Gravityy999/Proiect_InkTime/Hardware/Schematic_final.sch

## EAGLE design Hardware/Schematic_final.sch (2026-04-21)

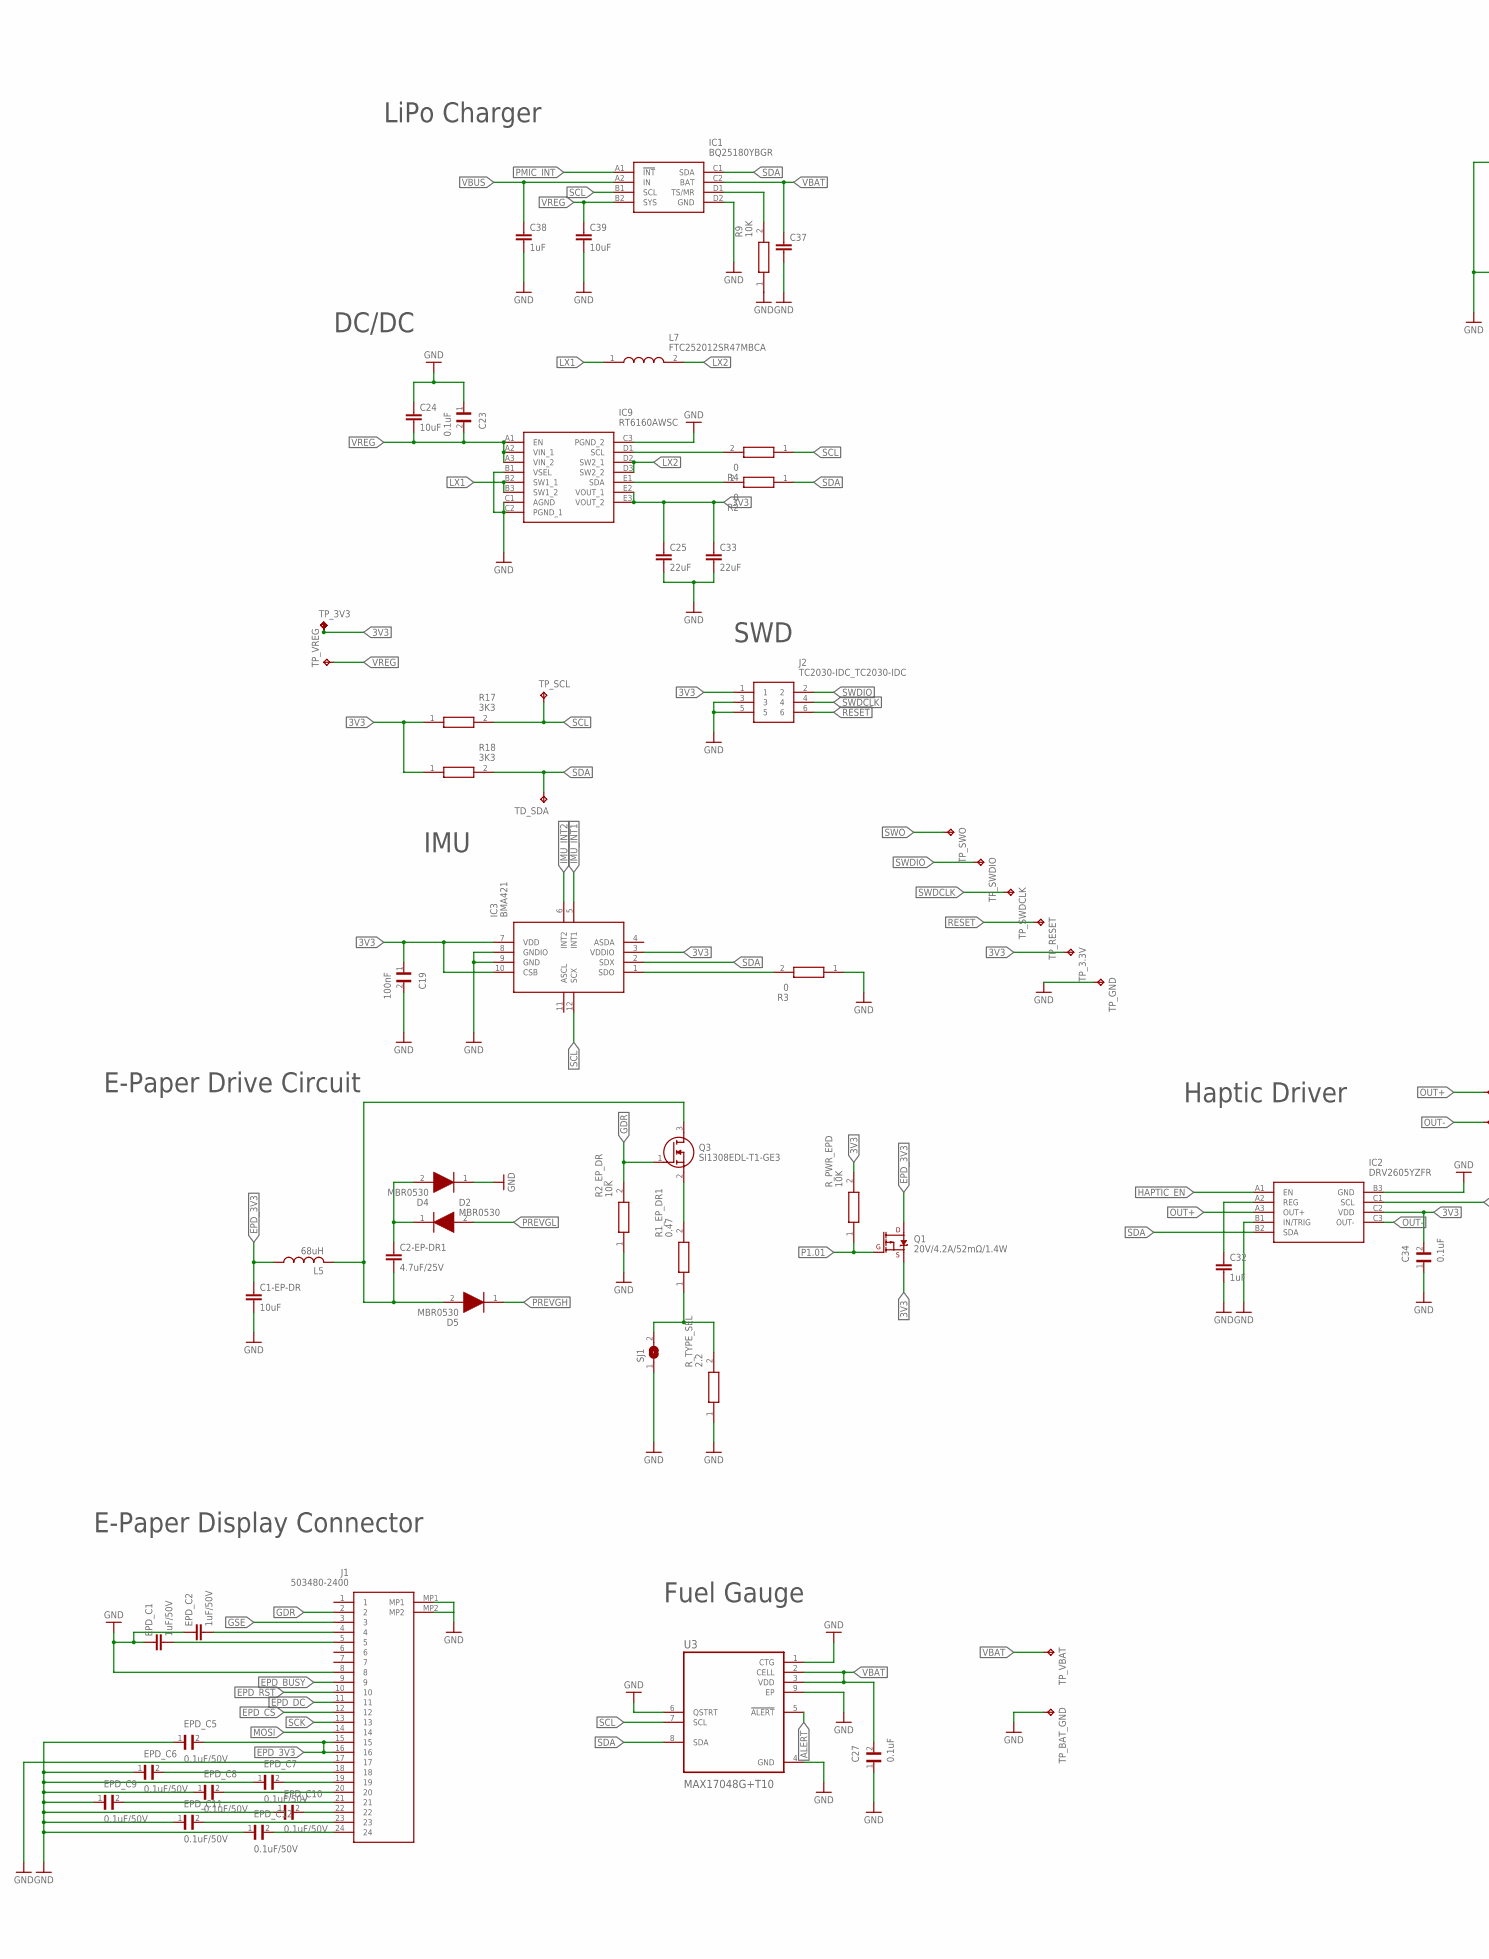
[picture p7: schematic Schematic_final.sch, part in row 1, column 1]

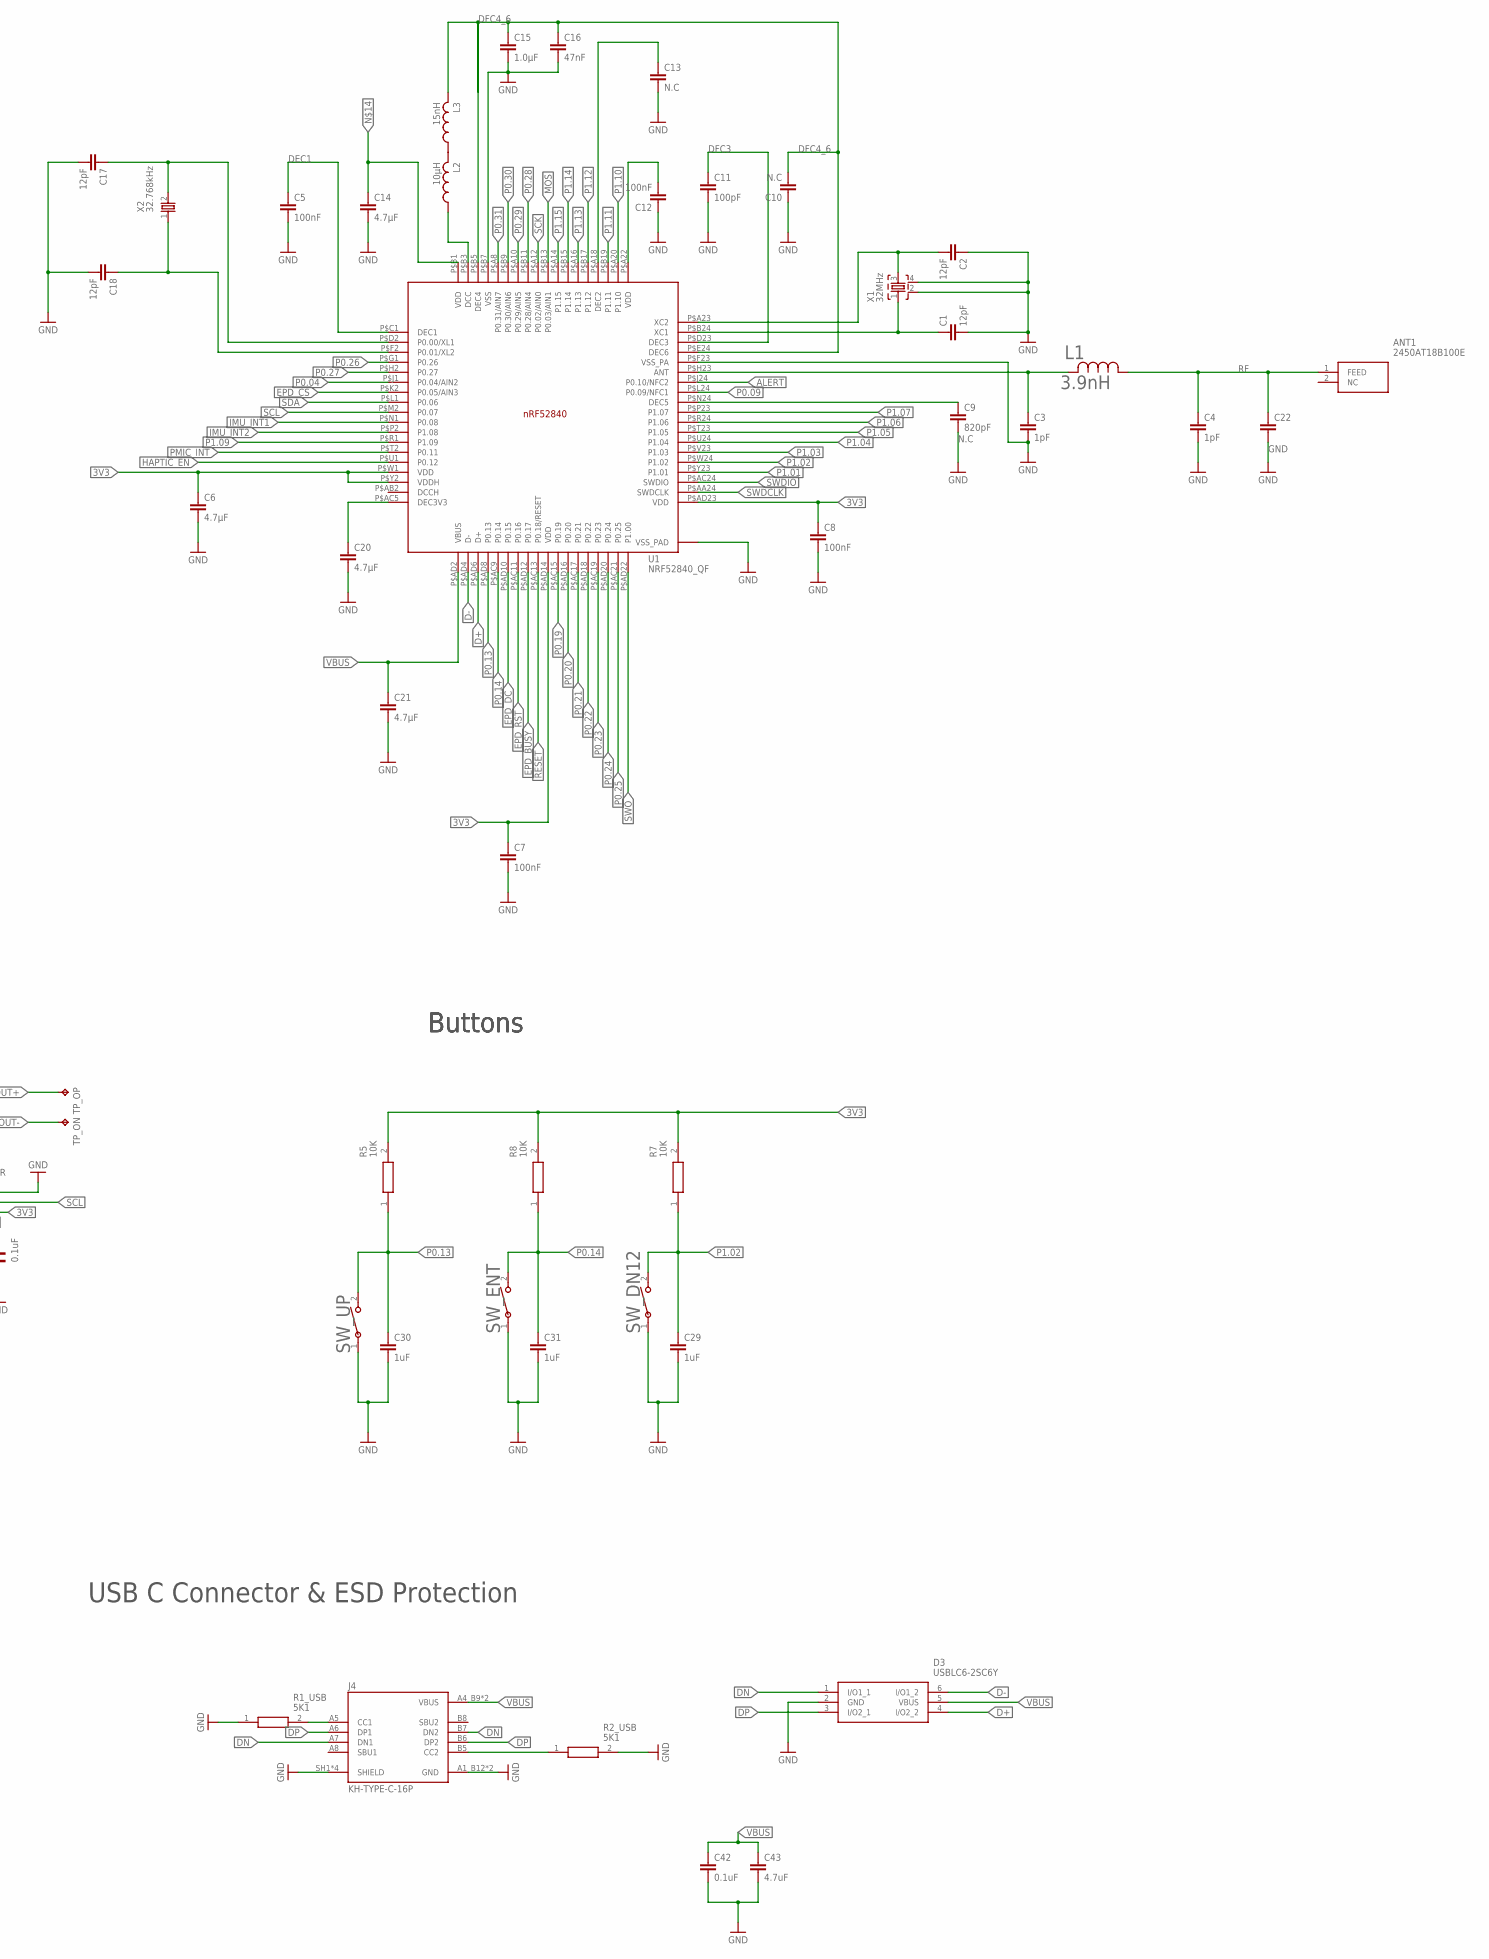
[picture p8: schematic Schematic_final.sch, part in row 1, column 2]

Parts:
ANT1: 2450AT18B100E; 2450AT18B100E_ANTC3216X140N
C1, C2, C17, C18: 12pF; NORDIC_NRF_3_RESC0201_L
C1-EP-DR: 10uF; PERFECT_0402_0402
C2-EP-DR1: 4.7uF/25V; PERFECT_0402_0402
C3, C4: 1pF; NORDIC_NRF_3_RESC0201_L
C5, C7, C8, C12: 100nF; NORDIC_NRF_3_RESC0201_L
C6, C20, C21: 4.7µF; ESP32_C6_LIBRARY_1_ESP32_WROVER_EAGLE-LTSPICE_C0402
C9: 820pF; NORDIC_NRF_3_RESC0201_L
C10, C13: N.C; NORDIC_NRF_3_RESC0201_L
C11: 100pF; NORDIC_NRF_3_RESC0201_L
C14: 4.7µF; PERFECT_0402_0402
C15: 1.0µF; PERFECT_0402_0402
C16: 47nF; NORDIC_NRF_3_RESC0201_L
C19: 100nF; GRM011R60J152KE01L_2_CAPC0201X13N
C22: NORDIC_NRF_3_CAPACITOR_0201_L; NORDIC_NRF_3_RESC0201_L
C23: 0.1uF; GRM011R60J152KE01L_2_CAPC0201X13N
C24, C39: 10uF; ESP32_C6_LIBRARY_1_ESP32_WROVER_EAGLE-LTSPICE_C0402
C25, C33: 22uF; ESP32_C6_LIBRARY_1_ESP32_WROVER_EAGLE-LTSPICE_C0402
C27, C34: 0.1uF; GRM011R60J152KE01L_1_0201
C29, C30, C31, C38: 1uF; ESP32_C6_LIBRARY_1_ESP32_WROVER_EAGLE-LTSPICE_C0402
C32: 1uF; PERFECT_0402_0402
C37: ESP32_C6_LIBRARY_1_ESP32_WROVER_EAGLE-LTSPICE_CC0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; ESP32_C6_LIBRARY_1_ESP32_WROVER_EAGLE-LTSPICE_C0402
C42: 0.1uF; NORDIC_NRF_3_RESC0201_L
C43: 4.7uF; ESP32_C6_LIBRARY_1_ESP32_WROVER_EAGLE-LTSPICE_C0402
D2, D4, D5: MBR0530; ESP32_C6_LIBRARY_5_SOD3716X135N
D3: USBLC6-2SC6Y; ESP32_C6_LIBRARY_3_SOT95P280X145-6N
EPD_C1, EPD_C2: 1uF/50V; ESP32_C6_LIBRARY_1_ESP32_WROVER_EAGLE-LTSPICE_C0402
EPD_C5, EPD_C6, EPD_C7, EPD_C8, EPD_C9, EPD_C10, EPD_C11, EPD_C12: 0.1uF/50V; GRM011R60J152KE01L_1_0201
IC1: BQ25180YBGR; BQ25180YBGR_BGA8C40P2X4_100X155X50
IC2: DRV2605YZFR; DRV2605YZFR_BGA9C50P3X3_144X144X62
IC3: BMA421; BMA423_BMA423
IC9: RT6160AWSC; RT6160AWSC_BGA15C40P3X5_140X230X60
J1: 503480-2400; 503480-2400_5034802400
J2: TC2030-IDC_TC2030-IDC; TC2030-IDC_TC2030IDC
J4: KH-TYPE-C-16P; KH-TYPE-C-16P_KINGHELM_KH-TYPE-C-16P
L1: 3.9nH; ESP32_C6_LIBRARY_2_IND_4828-WE-TPC_WRE
L2: 10µH; NORDIC_NRF_2_RESC0402_L
L3: 15nH; NORDIC_NRF_2_RESC0402_L
L5: 68uH; NORDIC_NRF_2_RESC0402_L
L7: FTC252012SR47MBCA; MLP2016SR47MT0S1_INDC2016X100N
Q1: 20V/4.2A/52mΩ/1.4W; ESP32_C6_LIBRARY_4_ESP32_C6_LIBRARY_4_ESP32_C6_LIBRARY_4_ES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
Q3: SI1308EDL-T1-GE3; ESP32_C6_LIBRARY_6_SOT65P210X110-3N
R1_EP_DR1: 0.47; CPF0201D7K68C1_0201
R1_USB, R2_USB: 5K1; CPF0201D7K68C1_0201
R2, R3, R4: 0; CPF0201D7K68C1_0201
R2_EP_DR, R5, R7, R8, R9: 10K; CPF0201D7K68C1_0201
R17, R18: 3K3; CPF0201D7K68C1_0201
R_PWR_EPD: 10K; CPF0201D7K68C1_0201
R_TYPE_SEL: 2.2; CPF0201D7K68C1_0201
SJ1: ESP32_C6_LIBRARY_7_JUMPER_SJ
SW_DN12: 2025-10-22_07-23-44_LIBRARY_EVP-AKE31ASW_EVP-AKE3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; 2025-10-22_07-23-44_LIBRARY_SW_EVP-AKE31A_PAN
SW_ENT: 2025-10-22_07-23-44_LIBRARY_EVP-AKE31ASW_EVP-AKE3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; 2025-10-22_07-23-44_LIBRARY_SW_EVP-AKE31A_PAN
SW_UP: 2025-10-22_07-23-44_LIBRARY_EVP-AKE31ASW_EVP-AKE3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; 2025-10-22_07-23-44_LIBRARY_SW_EVP-AKE31A_PAN
TD_SDA: HECTOR_WATCH_1_TPTP20R; HECTOR_WATCH_1_TP20R
TP1, TP2: HECTOR_WATCH_1_TPTP20R; HECTOR_WATCH_1_TP20R
TP_3.3V, TP_3V3: HECTOR_WATCH_1_TPTP20R; HECTOR_WATCH_1_TP20R
TP_BAT_GND: HECTOR_WATCH_1_TPTP20R; HECTOR_WATCH_1_TP20R
TP_GND: HECTOR_WATCH_1_TPTP20R; HECTOR_WATCH_1_TP20R
TP_ON: HECTOR_WATCH_1_TPTP20R; HECTOR_WATCH_1_TP20R
TP_OP: HECTOR_WATCH_1_TPTP20R; HECTOR_WATCH_1_TP20R
TP_RESET: HECTOR_WATCH_1_TPTP20R; HECTOR_WATCH_1_TP20R
TP_SCL: HECTOR_WATCH_1_TPTP20R; HECTOR_WATCH_1_TP20R
TP_SWDCLK: HECTOR_WATCH_1_TPTP20R; HECTOR_WATCH_1_TP20R
TP_SWDIO: HECTOR_WATCH_1_TPTP20R; HECTOR_WATCH_1_TP20R
TP_SWO: HECTOR_WATCH_1_TPTP20R; HECTOR_WATCH_1_TP20R
TP_VBAT: HECTOR_WATCH_1_TPTP20R; HECTOR_WATCH_1_TP20R
TP_VREG: HECTOR_WATCH_1_TPTP20R; HECTOR_WATCH_1_TP20R
U1: NRF52840_QF; NORDIC_NRF_4_AQFN50P700X700X85_HS-74N
U3: MAX17048G+T10; ESP32_C6_LIBRARY_SON50P200X200X80-9N
X1: 32MHz; NORDIC_NRF_BT-XTAL_2016_N
X2: 32.768kHz; NORDIC_NRF_1_XTAL_3215_N

Connections:
3V3: C6.1, C7.1, C8.1, C19.1, C25.1, C33.1, C34.2, IC2.C2 (VDD), IC3.3 (VDDIO), IC3.7 (VDD), IC3.10 (CSB), IC9.E2 (VOUT_1), IC9.E3 (VOUT_2), J2.1, Q1.2 (S), R5.2, R7.2, R8.2, R17.1, R18.1, R_PWR_EPD.2, TP1.TP, TP2.TP, TP_3.3V.TP, TP_3V3.TP, U1.P$AD14 (VDD), U1.P$AD23 (VDD), U1.P$W1 (VDD), U1.P$Y2 (VDDH)
ALERT: U1.P$J24 (P0.10/NFC2), U3.5 (!ALERT)
D+: D3.4 (I/O2_2)
D-: D3.6 (I/O1_2), U1.P$AD4 (D-)
DEC1: C5.1, U1.P$C1 (DEC1)
DFC3: C11.1, U1.P$D23 (DEC3)
DFC4_6: C10.2, C15.1, C16.1, L3.2, U1.P$B5 (DEC4), U1.P$E24 (DEC6)
DN: D3.1 (I/O1_1), J4.A7 (DN1), J4.B7 (DN2)
DP: D3.3 (I/O2_1), J4.A6 (DP1), J4.B6 (DP2)
EPD_3V3: C1-EP-DR.1, EPD_C5.2, J1.15, J1.16, L5.1, Q1.3 (D)
EPD_BUSY: J1.9, U1.P$AC11 (P0.16)
EPD_CS: J1.12, U1.P$K2 (P0.05/AIN3)
EPD_DC: J1.11, U1.P$AC9 (P0.14)
EPD_RST: J1.10, U1.P$AD10 (P0.15)
GDR: J1.2, Q3.1 (G), R2_EP_DR.2
GND: C1.2, C1-EP-DR.2, C2.1, C3.2, C4.2, C5.2, C6.2, C7.2, C8.2, C10.1, C11.2, C12.1, C13.2, C14.2, C15.2, C16.2, C17.2, C18.2, C19.2, C20.2, C21.2, C22.2, C23.1, C24.1, C25.2, C27.1, C29.2, C30.2, C31.2, C32.2, C33.2, C34.1, C37.2, C38.2, C39.2, C42.2, C43.2, D3.2 (GND), D4.1 (K), EPD_C1.1, EPD_C2.1, EPD_C5.1, EPD_C6.1, EPD_C7.1, EPD_C8.1, EPD_C9.1, EPD_C10.1, EPD_C11.1, EPD_C12.1, IC1.D2 (GND), IC2.B1 (IN/TRIG), IC2.B3 (GND), IC3.8 (GNDIO), IC3.9 (GND), IC9.B1 (VSEL), IC9.C1 (AGND), IC9.C2 (PGND_1), IC9.C3 (PGND_2), J1.8, J1.17, J1.MP1, J2.3, J2.5, J4.A1_B12 (GND), J4.SH1 (SHIELD), R1_USB.1, R2_EP_DR.1, R2_USB.2, R3.1, R9.1, R_TYPE_SEL.1, SJ1.1, SW_DN12.1, SW_ENT.1, SW_UP.1, TP_BAT_GND.TP, TP_GND.TP, U1.P$74 (VSS_PAD), U1.P$B7 (VSS), U1.P$F23 (VSS_PA), U3.1 (CTG), U3.4 (GND), U3.6 (QSTRT), U3.9 (EP), X1.2, X1.4
GSE: J1.3
HAPTIC_EN: IC2.A1 (EN), U1.P$U1 (P0.12)
IMU_INT1: IC3.5 (INT1), U1.P$N1 (P0.08)
IMU_INT2: IC3.6 (INT2), U1.P$P2 (P1.08)
LX1: IC9.B2 (SW1_1), IC9.B3 (SW1_2)
LX2: IC9.D2 (SW2_1), IC9.D3 (SW2_2)
MOS: U1.P$B13 (P0.03/AIN1)
MOSI: J1.14
unnamed: IC3.1 (SDO), R3.2
unnamed: IC1.D1 (TS/MR), R9.2
unnamed: IC9.D1 (SCL), R4.2
unnamed: IC9.E1 (SDA), R2.2
unnamed: C17.1, U1.P$D2 (P0.00/XL1), X2.2
unnamed: C18.1, U1.P$F2 (P0.01/XL2), X2.1
unnamed: C20.1, U1.P$AC5 (DEC3V3)
unnamed: C9.1, U1.P$N24 (DEC5)
unnamed: C3.1, L1.2, U1.P$H23 (ANT)
unnamed: C1.1, U1.P$B24 (XC1), X1.1
unnamed: C2.2, U1.P$A23 (XC2), X1.3
unnamed: C14.1, U1.P$B1 (VDD)
unnamed: L2.1, U1.P$B3 (DCC)
unnamed: L2.2, L3.1
unnamed: C13.1, U1.P$A18 (DEC2)
unnamed: C12.2, U1.P$A22 (VDD)
unnamed: C2-EP-DR1.2, D5.2 (A), L5.2, Q3.3 (D)
unnamed: C2-EP-DR1.1, D2.1 (K), D4.2 (A)
unnamed: Q3.2 (S), R1_EP_DR1.2
unnamed: R1_EP_DR1.1, R_TYPE_SEL.2, SJ1.2
unnamed: EPD_C2.2, J1.4
unnamed: EPD_C1.2, J1.5
unnamed: EPD_C6.2, J1.18
unnamed: EPD_C7.2, J1.19
unnamed: EPD_C8.2, J1.20
unnamed: EPD_C9.2, J1.21
unnamed: EPD_C10.2, J1.22
unnamed: EPD_C11.2, J1.23
unnamed: EPD_C12.2, J1.24
unnamed: C32.1, IC2.A2 (REG)
unnamed: J4.A5 (CC1), R1_USB.2
unnamed: J4.B5 (CC2), R2_USB.1
N.C: C9.2
OUT+: IC2.A3 (OUT+), TP_OP.TP
OUT-: IC2.C3 (OUT-), TP_ON.TP
P0.04: U1.P$J1 (P0.04/AIN2)
P0.09: U1.P$L24 (P0.09/NFC1)
P0.13: C30.1, R5.1, SW_UP.2, U1.P$AD6 (D+)
P0.14: C31.1, R8.1, SW_ENT.2, U1.P$AD8 (P0.13)
P0.19: U1.P$AC15 (P0.19)
P0.20: U1.P$AD16 (P0.20)
P0.21: U1.P$AC17 (P0.21)
P0.22: U1.P$AD18 (P0.22)
P0.23: U1.P$AC19 (P0.23)
P0.24: U1.P$AD20 (P0.24)
P0.25: U1.P$AC21 (P0.25)
P0.26: U1.P$G1 (P0.26)
P0.27: U1.P$H2 (P0.27)
P0.28: U1.P$B11 (P0.28/AIN4)
P0.29: U1.P$A10 (P0.29/AIN5)
P0.30: U1.P$B9 (P0.30/AIN6)
P0.31: U1.P$A8 (P0.31/AIN7)
P1.01: Q1.1 (G), R_PWR_EPD.1, U1.P$Y23 (P1.01)
P1.02: C29.1, R7.1, SW_DN12.2, U1.P$W24 (P1.02)
P1.03: U1.P$V23 (P1.03)
P1.04: U1.P$U24 (P1.04)
P1.05: U1.P$T23 (P1.05)
P1.06: U1.P$R24 (P1.06)
P1.07: U1.P$P23 (P1.07)
P1.09: U1.P$R1 (P1.09)
P1.10: U1.P$A20 (P1.10)
P1.11: U1.P$B19 (P1.11)
P1.12: U1.P$B17 (P1.12)
P1.13: U1.P$A16 (P1.13)
P1.14: U1.P$B15 (P1.14)
P1.15: U1.P$A14 (P1.15)
PMIC_INT: IC1.A1 (!INT), U1.P$T2 (P0.11)
PREVGH: D5.1 (K)
PREVGL: D2.2 (A)
RESET: J2.6, TP_RESET.TP, U1.P$AC13 (P0.18/RESET)
RF: ANT1.1 (FEED), C4.1, C22.1, L1.1
SCK: J1.13, U1.P$A12 (P0.02/AIN0)
SCL: IC1.B1 (SCL), IC2.C1 (SCL), IC3.12 (SCX), R4.1, R17.2, TP_SCL.TP, U1.P$M2 (P0.07), U3.7 (SCL)
SDA: IC1.C1 (SDA), IC2.B2 (SDA), IC3.2 (SDX), R2.1, R18.2, TD_SDA.TP, U1.P$L1 (P0.06), U3.8 (SDA)
SWDCLK: J2.4, TP_SWDCLK.TP, U1.P$AA24 (SWDCLK)
SWDIO: J2.2, TP_SWDIO.TP, U1.P$AC24 (SWDIO)
SWO: TP_SWO.TP, U1.P$AD22 (P1.00)
VBAT: C27.2, C37.1, IC1.C2 (BAT), TP_VBAT.TP, U3.2 (CELL), U3.3 (VDD)
VBUS: C21.1, C38.1, C42.1, C43.1, D3.5 (VBUS), IC1.A2 (IN), J4.A4_B9 (VBUS), U1.P$AD2 (VBUS)
VREG: C23.2, C24.2, C39.1, IC1.B2 (SYS), IC9.A1 (EN), IC9.A2 (VIN_1), IC9.A3 (VIN_2), TP_VREG.TP

Notes on the sheet:
LiPo Charger
DC/DC
SWD
IMU
E-Paper Drive Circuit
E-Paper Display Connector
Fuel Gauge
Haptic Driver
Buttons
USB C Connector & ESD Protection
